kankrittapon/marine-tracker/docs/REFACTOR_NOTES.md

# Documentation Refactor Notes

## Single Source of Truth

- `STATUS.md`: current phase, current batch, blockers, progress, and next action.
- `PROJECT_MASTER_PLAN.md`: static roadmap, phase definitions, milestones, and exit criteria only.
- `ENGINEERING_RULEBOOK.md`: mandatory engineering rules.
- `ENGINEERING_INDEX.md`: document routing and ownership map.

## Resolved Conflicts

- Removed live status from `PROJECT_MASTER_PLAN.md`.
- Marked ADR-008 and ADR-009 approved.
- Updated ADR-003, ADR-005, ADR-006, and ADR-007 implementation status.
- Schematic work now loads the implementation roadmap and recovery specifications when required.
